jdeguire/pjcontroller/firmware/common/sharedmem.c

/* Copyright © 2011-2013 Jesse DeGuire
 *
 * This file is part of Projector Controller.
 *
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
 * File:   sharedmem.c
 * Author: Jesse DeGuire
 *
 * Used for routines and memory shared between the PJC Bootloader and the application.
 */

#include "sharedmem.h"
#include "watchdog.h"
#include "misc.h"
#include <util/crc16.h>
#include <avr/interrupt.h>

// Not initialized by the startup module, so that memory contents are retained after a watchdog
// reset.  Note that the memory state is not trustworthy for other reset sources.
static volatile bool m_loadApplication __attribute__((section(".shareddata")));


/* Return True if the application reset the device (using the watchdog) and requested that the
 * bootloader restart the app.  If the device was _not_ reset by the watchdog, then restart the app
 * so that powering up the device runs the app as exptected.
 */
bool AppRestartRequested()
{
	return (!ResetByWatchdog()  ||  (ResetByWatchdog()  &&  m_loadApplication));
}

/* Clear the request to restart the app on reset.  This is done in the bootloader so that an
 * unintentional watchdog reset will land in the bootloader rather than restarting the (probably)
 * faulty application.
 */
void ClearAppRestartRequest()
{
	m_loadApplication = false;
}

/* Restart the application by requesting the bootloader to restart the app, enabling the shortest
 * watchdog time, and looping until the device restarts.  Note that other conditions (such as a bad
 * checksum) can still cause the bootloader to not start the app.
 */
void RestartApp()
{
	cli();
	m_loadApplication = true;
    wdt_enable(WDTO_15MS);
	for(;;) ;
}

/* Restart and stay in the bootloader by enabling the shortest watchdog timer and running an
 * infinite loop.
 */
void RestartBootloader()
{
	cli();
	m_loadApplication = false;
    wdt_enable(WDTO_15MS);
	for(;;)	;
}

/* Calculate 16-bit CRC for everything in app space.
 */
uint16_t CalculateAppCRC()
{
	uint16_t crc = 0xFFFF;
	uint16_t addr;

	wdt_reset();

	for(addr = APP_SPACE_START; addr <= APP_SPACE_END; ++addr)
		crc = _crc_ccitt_update(crc, pgm_read_byte(addr));

	wdt_reset();

	return crc;
}
