jdeguire/pjcontroller/firmware/bootloader/main.c

/* Copyright © 2011-2013 Jesse DeGuire
 *
 * This file is part of Projector Controller.
 *
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
 * File:   main.c
 * Author: Jesse DeGuire
 *
 * Main code module for the bootloader.
 */

#include "regmap.h"
#include "uart.h"
#include "cmd.h"
#include "sharedmem.h"
#include "deviceprog.h"
#include "localcmd.h"
#include "watchdog.h"
#include "led.h"
#include <stdint.h>
#include <stdbool.h>
#include <avr/interrupt.h>
#include <util/delay.h>

#define UseBootloaderIVT() do{MCUCR = (1 << IVCE); MCUCR = (1 << IVSEL);} while(0)
#define UseAppIVT()        do{MCUCR = (1 << IVCE); MCUCR = 0;} while(0)

// Check the state of the bootloader pin, which is active high
// Uses GCC Statement Expressions; see http://gcc.gnu.org/onlinedocs/gcc/Statement-Exprs.html
#define BootloaderPinSet() ({DDRDbits.ddd4 = 0; PINDbits.pind4;})

typedef enum
{
	eBootOK      = 0,
	eBootPinSet,
	eBootRestart,
	eBootNoApp,
	eBootCRC
} bootstatus_t;

static bootstatus_t m_status;


/* Check if there is any reason why the bootloader should not start the app and sets 'm_status' to
 * indicate the reason.
 */
static void GetAppStartupStatus()
{
	m_status = eBootOK;

	if(BootloaderPinSet())
		m_status = eBootPinSet;
	else if(!AppRestartRequested())
		m_status = eBootRestart;
	else
	{
		uint16_t appkey;
		uint16_t appcrc;

		appkey = pgm_read_word(FLASHEND - 3);
		appcrc = pgm_read_word(FLASHEND - 1);

		if(appkey != APP_CHECKSUM_VALID)
			m_status = eBootNoApp;
		else if(appcrc != CalculateAppCRC())
			m_status = eBootCRC;
	}

	ClearAppRestartRequest();
}

/* Print a message stating why we're in the bootloader along with the value of m_status.  This is
 * done so that software can grab the number and print its own message.
 */
void PrintBootStatus()
{
	UART_TxChar('(');
	UART_TxHexByte((uint8_t)m_status);
	UART_TxChar(')');

	switch(m_status)
	{
		case eBootPinSet:
			UART_TxData_P(PSTR(" Bootloader pin set\r"), 20);
			break;
		case eBootRestart:
			UART_TxData_P(PSTR(" WDT reset\r"), 11);
			break;
		case eBootNoApp:
			UART_TxData_P(PSTR(" No app loaded\r"), 15);
			break;
		case eBootCRC:
			UART_TxData_P(PSTR(" Invalid CRC\r"), 13);
			break;
		default:
			break;
	}
}

/* Undo the modifications to registers that the bootloader did when starting up.  Do this before
 * jumping to the app after the bootloader has started up.
 */
void RewindSettings()
{
	cli();                    // disable interrupts
	wdt_reset();
	UseAppIVT();
	ClrYellowLED();

	// initial UART register values
	UCSR0C = (1 << UCSZ01) | (1 << UCSZ00);
	UCSR0B = 0;
	UCSR0A = 0;
	UBRR0H = 0;
	UBRR0L = 0;

	wdt_disable();
}


int main(void)
{
	GetAppStartupStatus();

	if(m_status == eBootOK)
		asm volatile("jmp 0x0");
	else
	{
		wdt_enable(WDTO_250MS);

		UART_Init();
		Cmd_InitInterface();
		RegisterBootloaderCommands();

		UseBootloaderIVT();
		sei();                    // enable interrupts

		InitLEDs();
		SetYellowLED();
		PrintBootStatus();
		wdt_reset();

		while(true)
		{
			wdt_reset();
			Cmd_ProcessInterface();
		}
	}
}
